ParthDhiman32/CRASHSENSE/PCB/Crashsense/Crashsense.kicad_sch

## KiCad design PCB/Crashsense/Crashsense.kicad_sch (2026-07-27)

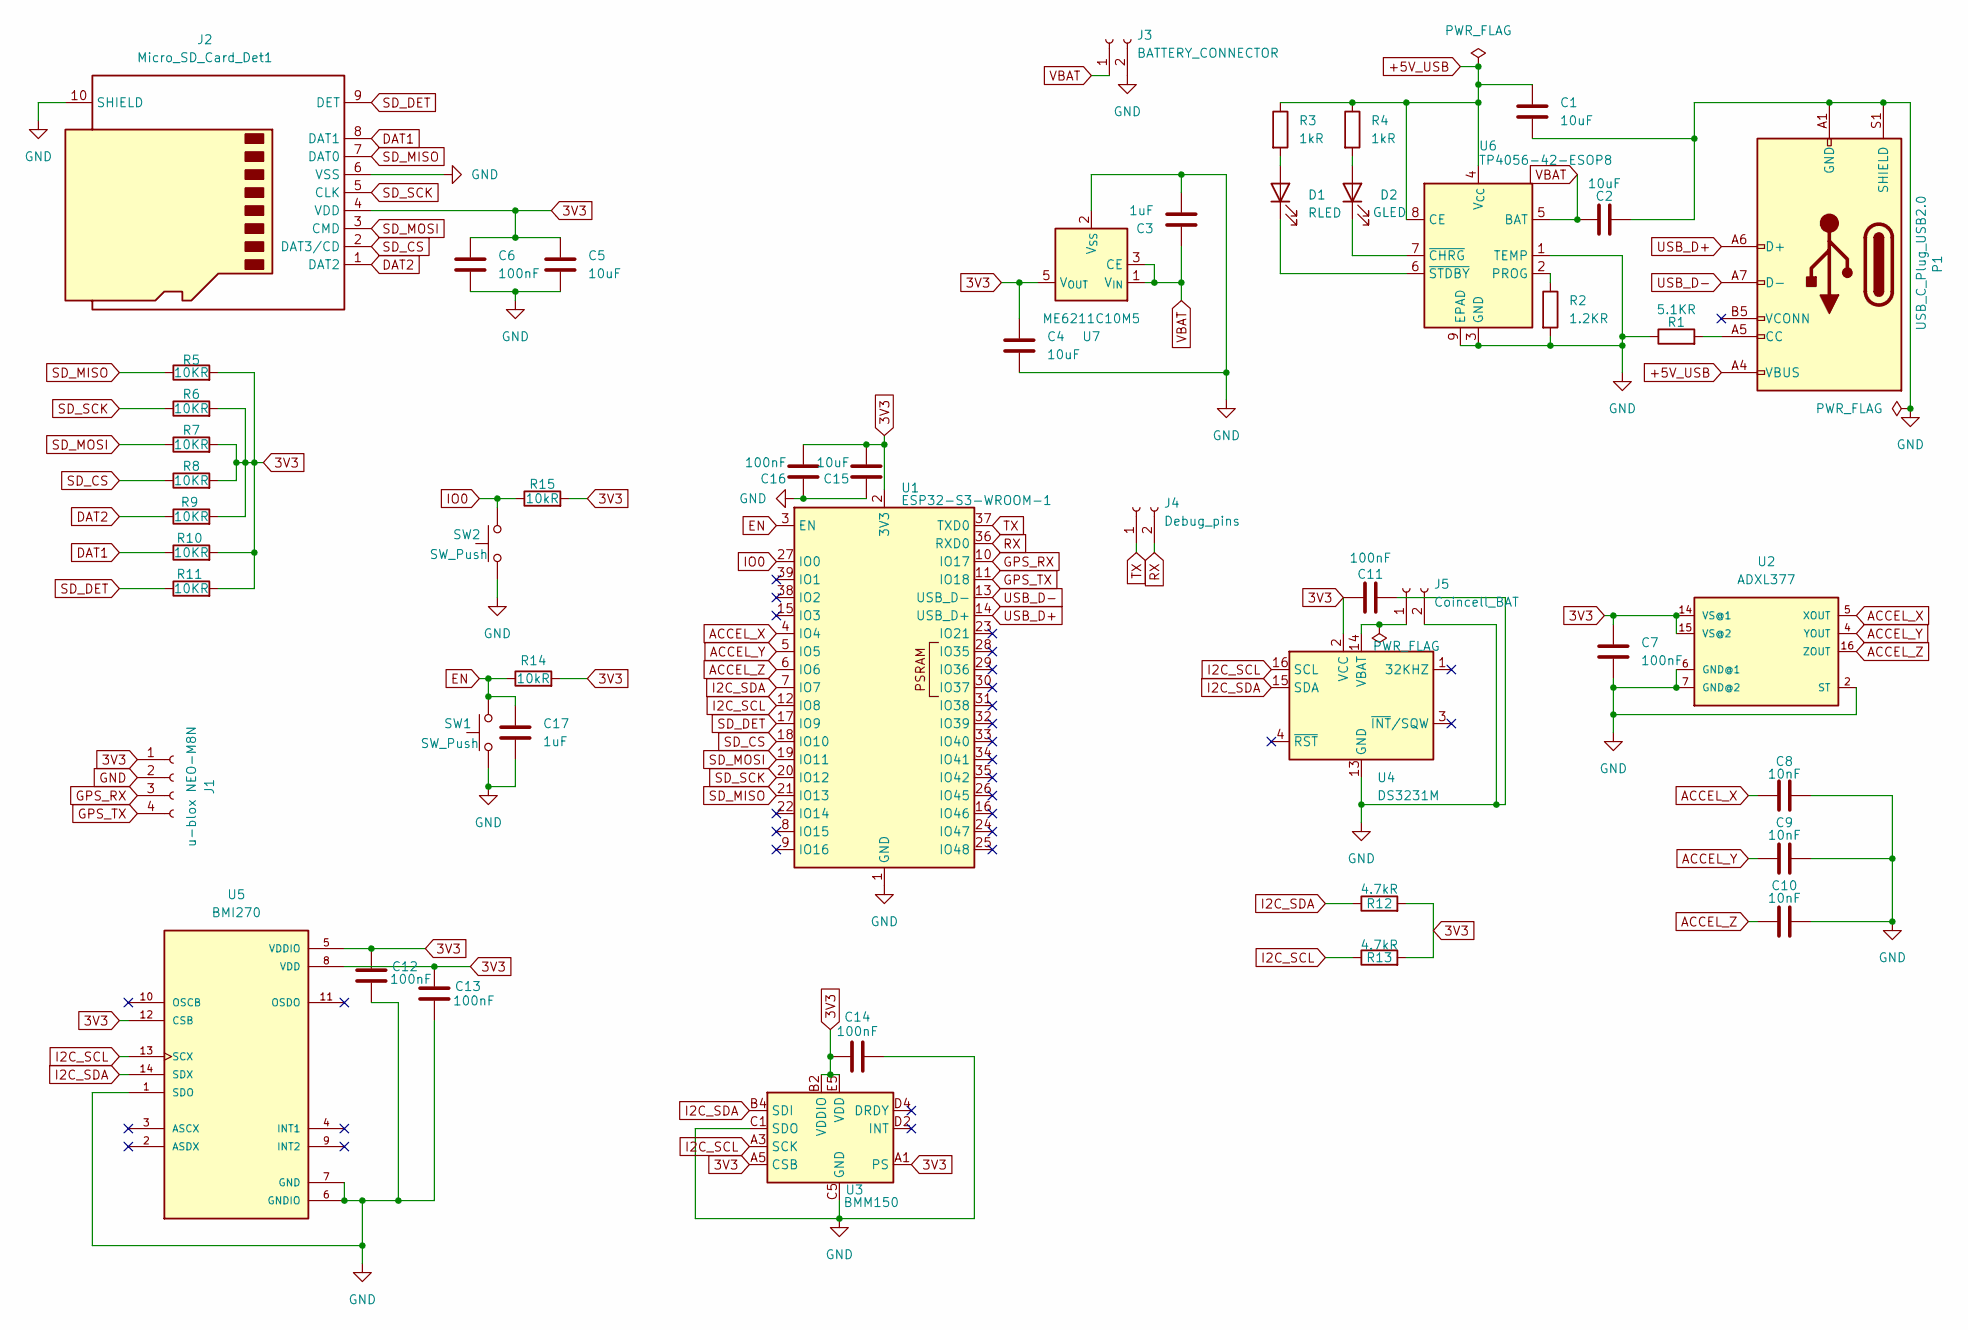
[picture p11: schematic Crashsense.kicad_sch]

Parts:
C1, C2, C4, C5, C15: 10uF; C_0805_2012Metric
C3, C17: 1uF; C_0805_2012Metric
C6, C7, C11, C12, C13, C14, C16: 100nF; C_0805_2012Metric
C8, C9, C10: 10nF; C_0805_2012Metric
D1: RLED; LED_0805_2012Metric
D2: GLED; LED_0805_2012Metric
J1: u-blox NEO-M8N; PinHeader_1x04_P2.54mm_Vertical
J2: Micro_SD_Card_Det1; microSD_HC_Hirose_DM3AT-SF-PEJM5
J3: BATTERY_CONNECTOR; JST_PH_B2B-PH-K_1x02_P2.00mm_Vertical
J4: Debug_pins; PinHeader_1x02_P2.54mm_Vertical
J5: Coincell_BAT; JST_PH_B2B-PH-K_1x02_P2.00mm_Vertical
P1: USB_C_Plug_USB2.0; USB_C_Receptacle_HRO_TYPE-C-31-M-12
R1: 5.1KR; R_0805_2012Metric
R2: 1.2KR; R_0805_2012Metric
R3, R4: 1kR; R_0805_2012Metric
R5, R6, R7, R8, R9, R10, R11: 10KR; R_0805_2012Metric
R12, R13: 4.7kR; R_0805_2012Metric
R14, R15: 10kR; R_0805_2012Metric
SW1, SW2: SW_Push; SW_SPST_SKQG_WithStem
U1: ESP32-S3-WROOM-1
U2: ADXL377; LFCSP-16-3X3
U3: BMM150; WLCSP-12_1.56x1.56mm_P0.4mm
U4: DS3231M; SOIC-16W_7.5x10.3mm_P1.27mm
U5: BMI270; XDCR_BMI270
U6: TP4056-42-ESOP8; SOIC-8-1EP_3.9x4.9mm_P1.27mm_EP2.41x3.3mm_ThermalVias
U7: ME6211C10M5; SOT-23-5

Connections:
3V3: C4.1, C5.1, C6.1, C7.1, C11.1, C12.1, C13.1, C14.1, C15.2, C16.2, J1.1, J2.4 (VDD), R5.2, R6.2, R7.2, R8.2, R9.2, R10.2, R11.2, R12.2, R13.2, R14.2, R15.2, U1.2 (3V3), U2.14 (VS@1), U2.15 (VS@2), U3.A1 (PS), U3.A5 (CSB), U3.B2 (VDDIO), U3.E5 (VDD), U4.2 (VCC), U5.5 (VDDIO), U5.8 (VDD), U5.12 (CSB), U7.5 (V_{OUT})
+5V_USB: C1.1, P1.A4 (VBUS), P1.A9 (VBUS), P1.B4 (VBUS), P1.B9 (VBUS), R3.1, R4.1, U6.4 (V_{CC}), U6.8 (CE)
ACCEL_X: C8.1, U1.4 (IO4), U2.5 (XOUT)
ACCEL_Y: C9.1, U1.5 (IO5), U2.4 (YOUT)
ACCEL_Z: C10.1, U1.6 (IO6), U2.16 (ZOUT)
DAT1: J2.8 (DAT1), R10.1
DAT2: J2.1 (DAT2), R9.1
EN: C17.1, R14.1, SW1.2, U1.3 (EN)
GND: C1.2, C2.2, C3.2, C4.2, C5.2, C6.2, C7.2, C8.2, C9.2, C10.2, C11.2, C12.2, C13.2, C14.2, C15.1, C16.1, C17.2, J1.2, J2.6 (VSS), J2.10 (SHIELD), J3.2, J5.2, P1.A1 (GND), P1.A12 (GND), P1.B1 (GND), P1.B12 (GND), P1.S1 (SHIELD), R1.1, R2.2, SW1.1, SW2.1, U1.1 (GND), U1.40 (GND), U1.41 (GND), U2.2 (ST), U2.6 (GND@1), U2.7 (GND@2), U3.C1 (SDO), U3.C5 (GND), U3.E1 (GND), U3.E3 (GND), U4.5 (GND), U4.6 (GND), U4.7 (GND), U4.8 (GND), U4.9 (GND), U4.10 (GND), U4.11 (GND), U4.12 (GND), U4.13 (GND), U5.1 (SDO), U5.6 (GNDIO), U5.7 (GND), U6.1 (TEMP), U6.3 (GND), U6.9 (EPAD), U7.2 (V_{SS})
GPS_RX: J1.3, U1.10 (IO17)
GPS_TX: J1.4, U1.11 (IO18)
I2C_SCL: R13.1, U1.12 (IO8), U3.A3 (SCK), U4.16 (SCL), U5.13 (SCX)
I2C_SDA: R12.1, U1.7 (IO7), U3.B4 (SDI), U4.15 (SDA), U5.14 (SDX)
IO0: R15.1, SW2.2, U1.27 (IO0)
unnamed: D1.1 (K), U6.6 (~STDBY)
unnamed: D1.2 (A), R3.2
unnamed: D2.1 (K), U6.7 (~CHRG)
unnamed: D2.2 (A), R4.2
unnamed: J5.1, U4.14 (VBAT)
unnamed: P1.A5 (CC), R1.2
unnamed: R2.1, U6.2 (PROG)
RX: J4.2, U1.36 (RXD0)
SD_CS: J2.2 (DAT3/CD), R8.1, U1.18 (IO10)
SD_DET: J2.9 (DET), R11.1, U1.17 (IO9)
SD_MISO: J2.7 (DAT0), R5.1, U1.21 (IO13)
SD_MOSI: J2.3 (CMD), R7.1, U1.19 (IO11)
SD_SCK: J2.5 (CLK), R6.1, U1.20 (IO12)
TX: J4.1, U1.37 (TXD0)
USB_D+: P1.A6 (D+), U1.14 (USB_D+)
USB_D-: P1.A7 (D-), U1.13 (USB_D-)
VBAT: C2.1, C3.1, J3.1, U6.5 (BAT), U7.1 (V_{IN}), U7.3 (CE)
